amonbenson/expad/docs/diagrams/jack-monitor-states.png

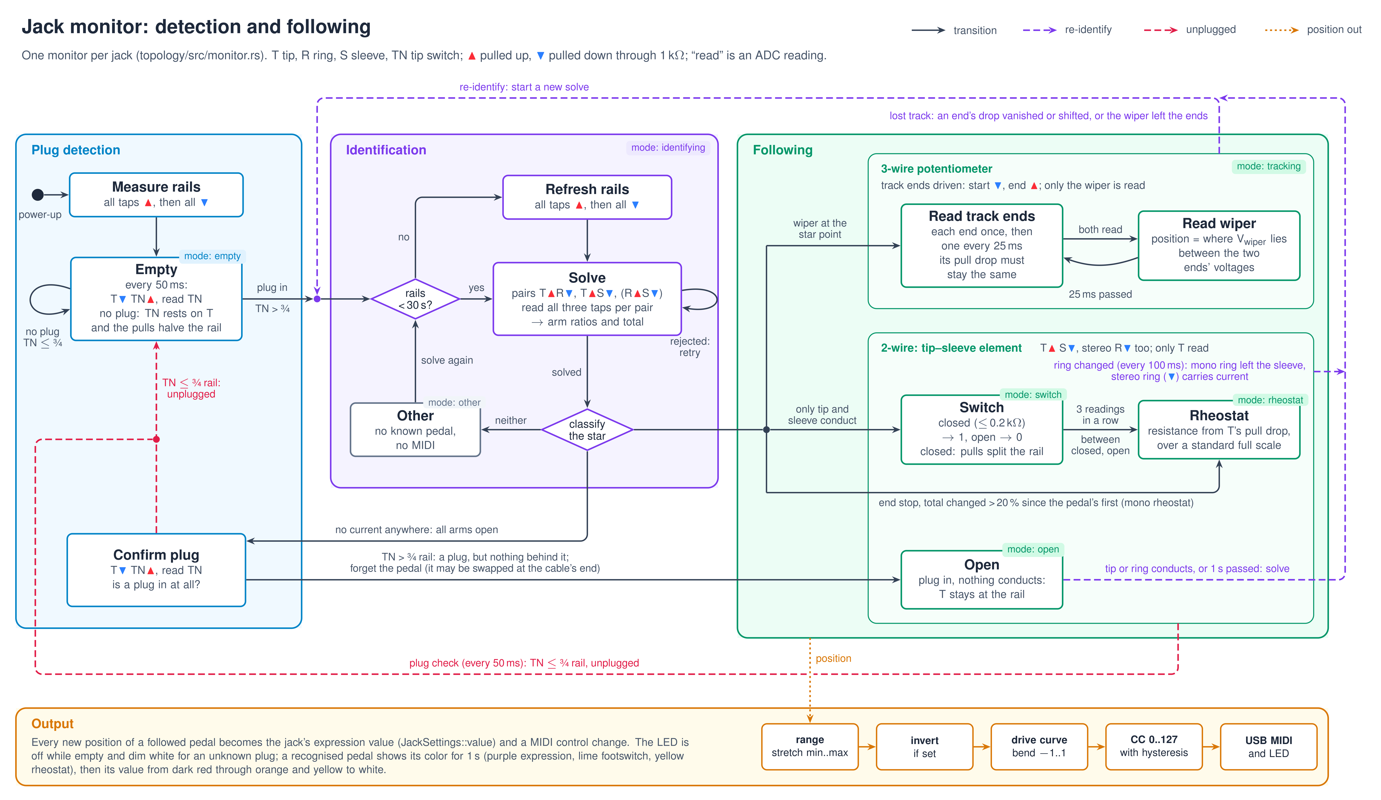
docs/diagrams/jack-monitor-states.png
