amonbenson/expad/report/05-results/chapter.tex

% !TEX root = ../main.tex

\chapter{Results}
\label{ch:results}

\scaffold{
  Chapter purpose: the evaluation the supervisor asked to be the main part, structured from the signal chain upward: board, supply and bus, ADC noise, position noise, timing, pedal types, and finally the requirements of the proposal. Each section names its setup and conditions (also in the captions), then states what the data shows; interpretation goes to \cref{ch:discussion}. The evaluation plan of milestone~1 listed supply quality, SPI signal quality, a functional self-test, identification of known networks, accuracy and linearity, and end-to-end latency; \cref{sec:results-requirements} closes the loop on that list.
}

\input{05-results/01-setup}
\input{05-results/02-self-test}
\input{05-results/03-supply}
\input{05-results/04-spi}
\input{05-results/05-adc-noise}
\input{05-results/06-position-noise}
\input{05-results/07-recognition-time}
\input{05-results/08-settling}
\input{05-results/09-update-rate}
\input{05-results/10-pedal-types}
\input{05-results/11-requirements}
