amonbenson/expad/measurements/supply_rail_measurement.xlsx

Setup | Division | Net | Image No. | Vrms Avg (mV) | Vrms Dev (mV) | Vpp Max (mV) | Vpp Dev (mV) | Cnt (VRMS1) | Cnt (Vpp1) | Timebase (screen) | CH1 scale (screen)
no Microcontroller | 10 ms | Vext | 3 | 0.83492 | 1.2122 | 15.86 | 1.3542 | 1000 | 1000 | 10.0ms | 1.00mV
no Microcontroller | 10 ms | +5V | 4 | 0.83071 | 1.1583 | 15.86 | 1.325 | 1000 | 1000 | 10.0ms | 1.00mV
no Microcontroller | 10 ms | +3.3V | 5 | 0.81165 | 1.1121 | 15.86 | 1.3814 | 1000 | 1000 | 10.0ms | 1.00mV
no Microcontroller | 10 ms | +2.5V | 11 | 0.3474 | 0.013996 | 2.015 | 0.093298 | 137 | 137 | 10.0ms | 1.00mV
no Microcontroller | 1 us | Vext | 8 | 1.1417 | 2.4585 | 19.384 | 2.2609 | 1000 | 1000 | 1.00us | 5.00mV
no Microcontroller | 1 us | +5V | 9 | 1.2469 | 2.6736 | 19.384 | 2.438 | 1000 | 1000 | 1.00us | 5.00mV
no Microcontroller | 1 us | +3.3V | 10 | 1.2288 | 2.567 | 19.384 | 2.6039 | 1000 | 1000 | 1.00us | 5.00mV
no Microcontroller | 1 us | +2.5V | 7 | 0.74243 | 0.094175 | 17.97 | 1.36 | 709 | 709 | 1.00us | 5.00mV
Idle/Detecting | 10 ms | Vext | 12 | 2.7243 | 0.12946 | 17.365 | 0.33486 | 176 | 176 | 10.0ms | 5.00mV
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
