amonbenson/expad/src/hal/adc/registers/control.rs

use num_enum::{IntoPrimitive, TryFromPrimitive};

use super::RegisterValue;
use super::mode::ChannelCount;

pub type Control = RegisterValue<0x02, 1>;

#[repr(u8)]
#[derive(Clone, Copy, Debug, IntoPrimitive, TryFromPrimitive)]
pub enum ChannelConfiguration {
    Single1 = 0b0000,
    Single2 = 0b0001,
    Single3 = 0b0010,
    Single4 = 0b0011,
    Single5 = 0b0100,
    Single6 = 0b0101,
    Single7 = 0b0110,
    Single8 = 0b0111,
    Diff1_2 = 0b1000,
    Diff3_4 = 0b1001,
    Diff5_6 = 0b1010,
    Diff7_8 = 0b1011,
    Diff9_10 = 0b1100,
    AInCom = 0b1101,
    RefInSingle9 = 0b1110,
    OpenSingle10 = 0b1111,
}

#[derive(Clone, Copy, Debug, PartialEq, Eq)]
pub enum Input {
    AIn(u8),
    AInCom,
    RefInPositive,
    RefInNegative,
    Open,
}

impl ChannelConfiguration {
    pub const fn single(input: u8, channel_count: ChannelCount) -> Option<Self> {
        match (input, channel_count) {
            (0, _) => Some(Self::Single1),
            (1, _) => Some(Self::Single2),
            (2, _) => Some(Self::Single3),
            (3, _) => Some(Self::Single4),
            (4, _) => Some(Self::Single5),
            (5, _) => Some(Self::Single6),
            (6, _) => Some(Self::Single7),
            (7, _) => Some(Self::Single8),
            (8, ChannelCount::Ten) => Some(Self::RefInSingle9),
            (9, ChannelCount::Ten) => Some(Self::OpenSingle10),
            _ => None,
        }
    }

    pub const fn differential(
        positive_input: u8,
        negative_input: u8,
        channel_count: ChannelCount,
    ) -> Option<Self> {
        match (positive_input, negative_input, channel_count) {
            (0, 1, _) => Some(Self::Diff1_2),
            (2, 3, _) => Some(Self::Diff3_4),
            (4, 5, _) => Some(Self::Diff5_6),
            (6, 7, _) => Some(Self::Diff7_8),
            (8, 9, ChannelCount::Ten) => Some(Self::Diff9_10),
            _ => None,
        }
    }

    pub fn inputs(self, channel_count: ChannelCount) -> (Input, Input) {
        use ChannelCount::{Eight, Ten};
        use Input::{AIn, AInCom, Open, RefInNegative, RefInPositive};

        match (self, channel_count) {
            (Self::Single1, _) => (AIn(0), AInCom),
            (Self::Single2, _) => (AIn(1), AInCom),
            (Self::Single3, _) => (AIn(2), AInCom),
            (Self::Single4, _) => (AIn(3), AInCom),
            (Self::Single5, _) => (AIn(4), AInCom),
            (Self::Single6, _) => (AIn(5), AInCom),
            (Self::Single7, _) => (AIn(6), AInCom),
            (Self::Single8, _) => (AIn(7), AInCom),
            (Self::Diff1_2, _) => (AIn(0), AIn(1)),
            (Self::Diff3_4, _) => (AIn(2), AIn(3)),
            (Self::Diff5_6, _) => (AIn(4), AIn(5)),
            (Self::Diff7_8, _) => (AIn(6), AIn(7)),
            (Self::Diff9_10, Eight) => (AIn(1), AIn(1)),
            (Self::Diff9_10, Ten) => (AIn(8), AIn(9)),
            (Self::AInCom, _) => (AInCom, AInCom),
            (Self::RefInSingle9, Eight) => (RefInPositive, RefInNegative),
            (Self::RefInSingle9, Ten) => (AIn(8), AInCom),
            (Self::OpenSingle10, Eight) => (Open, Open),
            (Self::OpenSingle10, Ten) => (AIn(9), AInCom),
        }
    }

    pub fn calibration_register(self, channel_count: ChannelCount) -> u8 {
        use ChannelCount::{Eight, Ten};

        match (self, channel_count) {
            (Self::Single1, _) => 1,
            (Self::Single2, _) => 2,
            (Self::Single3, _) => 3,
            (Self::Single4, _) => 4,
            (Self::Single5, Eight) => 1,
            (Self::Single5, Ten) => 5,
            (Self::Single6, Eight) => 2,
            (Self::Single6, Ten) => 1,
            (Self::Single7, Eight) => 3,
            (Self::Single7, Ten) => 2,
            (Self::Single8, Eight) => 4,
            (Self::Single8, Ten) => 3,
            (Self::Diff1_2, _) => 1,
            (Self::Diff3_4, _) => 2,
            (Self::Diff5_6, _) => 3,
            (Self::Diff7_8, _) => 4,
            (Self::Diff9_10, Eight) => 1,
            (Self::Diff9_10, Ten) => 5,
            (Self::AInCom, _) => 1,
            (Self::RefInSingle9, Eight) => 1,
            (Self::RefInSingle9, Ten) => 4,
            (Self::OpenSingle10, Eight) => 1,
            (Self::OpenSingle10, Ten) => 5,
        }
    }
}

#[repr(u8)]
#[derive(Clone, Copy, Debug, PartialEq, Eq, IntoPrimitive, TryFromPrimitive)]
pub enum Coding {
    Bipolar = 0b0,
    Unipolar = 0b1,
}

#[repr(u8)]
#[derive(Clone, Copy, Debug, IntoPrimitive, TryFromPrimitive)]
pub enum Range {
    V20mV = 0b000,
    V40mV = 0b001,
    V80mV = 0b010,
    V160mV = 0b011,
    V320mV = 0b100,
    V640mV = 0b101,
    V1_28V = 0b110,
    V2_56V = 0b111,
}

impl Range {
    pub const fn from_max_voltage(max_voltage: f32) -> Option<Self> {
        match max_voltage {
            v if v <= 0.020 => Some(Self::V20mV),
            v if v <= 0.040 => Some(Self::V40mV),
            v if v <= 0.080 => Some(Self::V80mV),
            v if v <= 0.160 => Some(Self::V160mV),
            v if v <= 0.320 => Some(Self::V320mV),
            v if v <= 0.640 => Some(Self::V640mV),
            v if v <= 1.28 => Some(Self::V1_28V),
            v if v <= 2.56 => Some(Self::V2_56V),
            _ => None,
        }
    }

    pub const fn voltage(self) -> f32 {
        match self {
            Self::V20mV => 0.020,
            Self::V40mV => 0.040,
            Self::V80mV => 0.080,
            Self::V160mV => 0.160,
            Self::V320mV => 0.320,
            Self::V640mV => 0.640,
            Self::V1_28V => 1.28,
            Self::V2_56V => 2.56,
        }
    }
}

impl Control {
    pub fn channel_configuration(&self) -> ChannelConfiguration {
        self.field(4, 4)
    }

    pub fn set_channel_configuration(&mut self, value: ChannelConfiguration) {
        self.set_field(4, 4, value);
    }

    pub fn coding(&self) -> Coding {
        self.field(3, 1)
    }

    pub fn set_coding(&mut self, value: Coding) {
        self.set_field(3, 1, value);
    }

    pub fn range(&self) -> Range {
        self.field(0, 3)
    }

    pub fn set_range(&mut self, value: Range) {
        self.set_field(0, 3, value);
    }
}
