amonbenson/expad/src/bin/expression_controller.rs

#![no_std]
#![no_main]

use core::cell::RefCell;

use defmt::{debug, info, unwrap, warn};
use embassy_executor::Spawner;
use embassy_rp::peripherals::{DMA_CH0, DMA_CH1, PIO0, PIO1, USB};
use embassy_rp::{bind_interrupts, dma, pio, usb};
use embassy_sync::blocking_mutex::Mutex;
use embassy_sync::blocking_mutex::raw::CriticalSectionRawMutex;
use embassy_sync::signal::Signal;
use embassy_time::{Duration, Instant};
use expad::board::{self, JACK_COUNT, JACKS};
use expad::hal::adc::AdcChainConfig;
use expad::hal::usb::{
    CableNumber, Channel as MidiChannel, ControlFunction, FromClamped, Message, U7, UsbMidi,
    UsbMidiConfig, UsbMidiDevice,
};
use expad::hal::wifi::AccessPointPeripherals;
#[cfg(not(feature = "no-wifi"))]
use expad::hal::wifi::{AccessPointConfig, start_access_point};
use expad::indicator::JackIndicators;
use expad::topology::scanner::{JackScanner, SettleConfig};
use expad::topology::{JackMode, JackReport, MonitorConfig, SolverConfig};
#[cfg(not(feature = "no-wifi"))]
use expad::web::spawn_web_server;
use expad::web::{ArmPull, INTERFACE, JackSettings, JackStatus, Settings, Status};

use {defmt_rtt as _, panic_probe as _};

/// How often the web interface is sent a new status. Positions update far more often than
/// a browser can show, so this only bounds the WebSocket traffic.
const STATUS_INTERVAL: Duration = Duration::from_millis(33);

/// How often the LEDs are rewritten with every jack's latest state.
const LED_INTERVAL: Duration = Duration::from_millis(20);

/// How often the number of position updates each jack received is logged.
const RATE_REPORT_INTERVAL: Duration = Duration::from_secs(5);

/// Highest value of a MIDI control change.
const MIDI_MAX_VALUE: u8 = 127;

/// How far the wiper has to move before a new control change is sent, as a fraction of
/// full travel. Slightly wider than one control change step, so a position resting between
/// two steps does not alternate between them.
const MIDI_HYSTERESIS: f32 = 0.6 / MIDI_MAX_VALUE as f32;

/// Control changes waiting to be sent. The measurement loop must never block on USB, so it
/// only replaces each jack's newest one, whether or not a host is listening.
static CONTROL_CHANGES: PendingControlChanges = PendingControlChanges::new();

bind_interrupts!(struct Irqs {
    PIO0_IRQ_0 => pio::InterruptHandler<PIO0>;
    PIO1_IRQ_0 => pio::InterruptHandler<PIO1>;
    DMA_IRQ_0 => dma::InterruptHandler<DMA_CH0>, dma::InterruptHandler<DMA_CH1>;
    USBCTRL_IRQ => usb::InterruptHandler<USB>;
});

#[unsafe(link_section = ".bi_entries")]
#[used]
pub static PICOTOOL_ENTRIES: [embassy_rp::binary_info::EntryAddr; 4] = [
    embassy_rp::binary_info::rp_program_name!(c"Expression Controller"),
    embassy_rp::binary_info::rp_program_description!(
        c"Continuously detects the resistor topology behind every jack, serves the web interface over WiFi and sends each pedal's position as a MIDI control change"
    ),
    embassy_rp::binary_info::rp_cargo_version!(),
    embassy_rp::binary_info::rp_program_build_attribute!(),
];

/// A control change the measurement loop has decided to send.
#[derive(Debug, Clone, Copy, defmt::Format)]
struct ControlChange {
    channel: u8,
    controller: u8,
    value: u8,
}

impl ControlChange {
    /// The MIDI message, unless the channel is out of range.
    fn message(self) -> Option<Message> {
        let channel = MidiChannel::try_from(self.channel).ok()?;
        Some(Message::ControlChange(
            channel,
            ControlFunction(U7::from_clamped(self.controller)),
            U7::from_clamped(self.value),
        ))
    }
}

#[derive(Debug, Clone, Copy)]
struct PendingJack {
    newest: Option<ControlChange>,
    unsent: bool,
}

#[derive(Debug)]
struct PendingState {
    jacks: [PendingJack; JACK_COUNT],
    /// Where the search for the next unsent control change starts, so that one busy jack
    /// cannot hold back the others.
    next_jack: usize,
}

/// The newest control change of every jack. A host only needs to know where each pedal is
/// now, so a newer control change replaces one still waiting, and nothing piles up while no
/// host is listening.
struct PendingControlChanges {
    state: Mutex<CriticalSectionRawMutex, RefCell<PendingState>>,
    updated: Signal<CriticalSectionRawMutex, ()>,
}

impl PendingControlChanges {
    const fn new() -> Self {
        let empty = PendingJack {
            newest: None,
            unsent: false,
        };
        Self {
            state: Mutex::new(RefCell::new(PendingState {
                jacks: [empty; JACK_COUNT],
                next_jack: 0,
            })),
            updated: Signal::new(),
        }
    }

    /// Makes `change` the jack's newest control change, to be sent next.
    fn publish(&self, jack: usize, change: ControlChange) {
        self.state.lock(|state| {
            state.borrow_mut().jacks[jack] = PendingJack {
                newest: Some(change),
                unsent: true,
            };
        });
        self.updated.signal(());
    }

    /// Forgets the jack's control change once nothing usable is plugged in any more.
    fn forget(&self, jack: usize) {
        self.state.lock(|state| {
            state.borrow_mut().jacks[jack] = PendingJack {
                newest: None,
                unsent: false,
            };
        });
    }

    /// Marks every jack's newest control change unsent again, so a newly connected host learns
    /// where every pedal is.
    fn resend_all(&self) {
        self.state.lock(|state| {
            for jack in &mut state.borrow_mut().jacks {
                jack.unsent = jack.newest.is_some();
            }
        });
        self.updated.signal(());
    }

    fn take_unsent(&self) -> Option<ControlChange> {
        self.state.lock(|state| {
            let mut state = state.borrow_mut();
            let jack = (0..JACK_COUNT)
                .map(|offset| (state.next_jack + offset) % JACK_COUNT)
                .find(|&jack| state.jacks[jack].unsent)?;
            state.jacks[jack].unsent = false;
            state.next_jack = (jack + 1) % JACK_COUNT;
            state.jacks[jack].newest
        })
    }

    /// Waits for a control change that has not been sent yet and takes it.
    async fn next_unsent(&self) -> ControlChange {
        loop {
            if let Some(change) = self.take_unsent() {
                return change;
            }
            self.updated.wait().await;
        }
    }
}

/// What the last control change sent for a jack was, and the expression value it was
/// quantized from.
#[derive(Debug, Clone, Copy)]
struct SentControlChange {
    value: f32,
    control: u8,
}

/// Quantizes an expression value in `0.0..=1.0` to a control change value.
fn control_value(value: f32) -> u8 {
    (value.clamp(0.0, 1.0) * MIDI_MAX_VALUE as f32 + 0.5) as u8
}

/// Whether `value` has moved far enough from what was last sent for its control change to be
/// worth sending, which also covers the very first reading of a jack.
fn worth_sending(sent: Option<SentControlChange>, value: f32, control: u8) -> bool {
    match sent {
        Some(sent) => control != sent.control && (value - sent.value).abs() > MIDI_HYSTERESIS,
        None => true,
    }
}

fn jack_status(report: &JackReport, settings: &JackSettings) -> JackStatus {
    let [tip, ring, sleeve] = report.voltages;
    JackStatus {
        mode: report.mode,
        position: report.position,
        value: report
            .position
            .map_or(0.0, |position| settings.value(position)),
        resistances: report.resistances,
        voltages: [tip, ring, sleeve, report.tip_switch_voltage],
        pulls: report.drives.map(ArmPull::from),
    }
}

/// Hands the settings' wiper choices to the scanner.
fn apply_wiper_settings<const S: usize, const A: usize, const J: usize>(
    scanner: &mut JackScanner<'_, S, A, J>,
    settings: &Settings,
) {
    for (jack, jack_settings) in settings.jacks.iter().enumerate().take(J) {
        scanner.set_preferred_wiper(jack, jack_settings.wiper.arm());
    }
}

/// Opens the WiFi access point and serves the web interface on it.
#[cfg(not(feature = "no-wifi"))]
async fn start_web_interface(spawner: Spawner, radio: AccessPointPeripherals<DMA_CH0>) {
    info!("Starting WiFi access point");
    let stack = start_access_point(spawner, radio, Irqs, AccessPointConfig::default()).await;
    spawn_web_server(spawner, stack);
}

/// Holds the CYW43439 in reset instead of starting it, so the radio draws no power during
/// electrical tests. The web interface's settings then stay at their defaults.
#[cfg(feature = "no-wifi")]
async fn start_web_interface(_spawner: Spawner, radio: AccessPointPeripherals<DMA_CH0>) {
    use embassy_rp::gpio::{Level, Output};
    use static_cell::StaticCell;

    info!("WiFi disabled at build time, holding the radio powered down");
    // The pin returns to an input as soon as its Output is dropped, so it has to outlive main.
    static RADIO_POWER: StaticCell<Output<'static>> = StaticCell::new();
    RADIO_POWER.init(Output::new(radio.power, Level::Low));
}

#[embassy_executor::main]
async fn main(spawner: Spawner) {
    let peripherals = embassy_rp::init(Default::default());

    start_web_interface(
        spawner,
        AccessPointPeripherals {
            pio: peripherals.PIO1,
            dma: peripherals.DMA_CH0,
            power: peripherals.PIN_23,
            data: peripherals.PIN_24,
            chip_select: peripherals.PIN_25,
            clock: peripherals.PIN_29,
        },
    )
    .await;

    info!("Initializing pull switches");
    let mut switches = board::pull_switches(
        peripherals.SPI1,
        peripherals.PIN_14,
        peripherals.PIN_15,
        peripherals.PIN_11,
        peripherals.PIN_13,
    );
    unwrap!(switches.clear());

    info!("Initializing ADCs");
    let mut adcs = board::adcs(
        peripherals.SPI0,
        peripherals.PIN_18,
        peripherals.PIN_19,
        peripherals.PIN_16,
        peripherals.PIN_17,
        peripherals.PIN_20,
        peripherals.PIN_21,
        peripherals.PIN_22,
    );
    let adc_config = AdcChainConfig::default()
        .with_channel_count(board::ADC_CHANNEL_COUNT)
        .with_reference_voltage(board::REFERENCE_VOLTAGE)
        .with_update_rate(board::ADC_UPDATE_RATE);
    unwrap!(adcs.init(adc_config).await);
    info!("ADC full scale: {}V", adcs.full_scale_voltage());

    info!("Initializing LED strip");
    let mut indicators = JackIndicators::new(
        board::leds(
            peripherals.PIO0,
            Irqs,
            peripherals.DMA_CH1,
            peripherals.PIN_6,
        ),
        JACKS.map(|jack| jack.led),
    );

    info!("Initializing USB MIDI");
    let (midi, usb_device) = UsbMidi::new(peripherals.USB, Irqs, UsbMidiConfig::default());
    spawner.spawn(unwrap!(run_usb(usb_device)));
    spawner.spawn(unwrap!(send_control_changes(midi)));

    let monitor_config = MonitorConfig::new(
        SolverConfig::from_voltage_noise(board::ADC_VOLTAGE_NOISE),
        board::PULL_RESISTANCE,
    );
    let settle_config = SettleConfig::new(
        board::INPUT_FILTER_CAPACITANCE,
        board::INPUT_FILTER_RESISTANCE,
    );
    let mut scanner = JackScanner::new(
        switches,
        adcs,
        settle_config,
        JACKS.map(|jack| jack.config()),
        monitor_config,
    );
    let mut settings_receiver = unwrap!(INTERFACE.settings.receiver());
    let mut settings = settings_receiver.get().await;

    apply_wiper_settings(&mut scanner, &settings);
    indicators.set_brightness(settings.led_brightness);

    let mut sent = [None::<SentControlChange>; JACK_COUNT];
    let mut modes = [JackMode::Empty; JACK_COUNT];
    let mut status_due = Instant::now();
    let mut leds_due = Instant::now();
    let mut rate_window_started = Instant::now();
    let mut position_updates = [0u32; JACK_COUNT];

    loop {
        if let Some(changed) = settings_receiver.try_changed() {
            info!("Settings changed: {}", changed);
            settings = changed;
            apply_wiper_settings(&mut scanner, &settings);
            indicators.set_brightness(settings.led_brightness);
            // Everything a control change is built from may have changed with them, so
            // let every jack send again rather than work out which parts still match.
            sent = [None; JACK_COUNT];
        }

        let changed = match scanner.step().await {
            Ok(changed) => changed,
            Err(error) => {
                warn!("Scanning the jacks failed: {}", error);
                continue;
            }
        };

        let now = Instant::now();
        for jack in (0..JACK_COUNT).filter(|&jack| changed[jack]) {
            let report = *scanner.report(jack);
            if report.mode != modes[jack] {
                info!(
                    "Jack {}: {}, {}, tip switch {}V",
                    jack, report.mode, report.resistances, report.tip_switch_voltage
                );
                modes[jack] = report.mode;
            }
            let followed = matches!(
                report.mode,
                JackMode::Tracking | JackMode::Switch | JackMode::Rheostat
            );
            if followed {
                position_updates[jack] += 1;
            }

            let jack_settings = &settings.jacks[jack];
            let value = report
                .position
                .map(|position| jack_settings.value(position));

            if let Some(value) = value {
                let control = control_value(value);
                if worth_sending(sent[jack], value, control) {
                    sent[jack] = Some(SentControlChange { value, control });
                    let change = ControlChange {
                        channel: jack_settings.midi_channel,
                        controller: jack_settings.midi_controller,
                        value: control,
                    };
                    CONTROL_CHANGES.publish(jack, change);
                }
            } else {
                sent[jack] = None;
                CONTROL_CHANGES.forget(jack);
            }

            let sent_value = sent[jack].map(|sent| sent.value);
            indicators.show(jack, report.mode, sent_value, now);
        }

        if now >= status_due {
            status_due = now + STATUS_INTERVAL;
            INTERFACE.status.sender().send(Status {
                jacks: core::array::from_fn(|jack| {
                    jack_status(scanner.report(jack), &settings.jacks[jack])
                }),
            });
        }

        if now >= leds_due {
            leds_due = now + LED_INTERVAL;
            indicators.update(now).await;
        }

        let window = now - rate_window_started;
        if window >= RATE_REPORT_INTERVAL {
            let window_millis = window.as_millis() as u32;
            let rates = position_updates.map(|updates| updates * 1000 / window_millis);
            info!("Position updates per second: {}", rates);
            position_updates = [0; JACK_COUNT];
            rate_window_started = now;
        }
    }
}

#[embassy_executor::task]
async fn run_usb(mut device: UsbMidiDevice) -> ! {
    device.run().await
}

/// Sends every jack's newest control change while a host is connected, and tells a newly
/// connected host where every pedal is.
#[embassy_executor::task]
async fn send_control_changes(mut midi: UsbMidi) -> ! {
    loop {
        midi.wait_connection().await;
        CONTROL_CHANGES.resend_all();

        loop {
            let change = CONTROL_CHANGES.next_unsent().await;
            let Some(message) = change.message() else {
                warn!("Ignoring {}, its MIDI channel is out of range", change);
                continue;
            };

            if let Err(error) = midi.send_message(CableNumber::Cable0, message).await {
                debug!("{} not sent: {}", change, error);
                break;
            }
        }
    }
}
